FPGA-Computer/Automatic-Audio-Switch/Eagle CAD/LT Spice Simulation/ADC scaling & filter.asc

C1: cap; 1n8
R1: res; 10K
R2: res; 10K
V1: voltage; SINE(0 3.3V 1000); AC 1
V2: voltage; 3.3V
Named nets: 0, vout
;tran 5ms
.ac dec 1000 1 1e6
