FPGA-Computer/Automatic-Audio-Switch/STM32F030/intfft.c

/*------------------------------------------------------------------------/
/  Integer DFT module
/-------------------------------------------------------------------------/
/
/  Copyright (C) 2010, ChaN, all right reserved.
/
/ * This software is a free software and there is NO WARRANTY.
/ * No restriction on use. You can use, modify and redistribute it for
/   personal, non-profit or commercial products UNDER YOUR RESPONSIBILITY.
/ * Redistributions of source code must retain the above copyright notice.
/
/-------------------------------------------------------------------------*/


#include "intfft.h"

const uint16_t Tbl_brev[] = {
#if   N_FFT == 64
	0,32,16,48,8,40,24,56,4,36,20,52,12,44,28,60,2,34,18,50,10,42,26,58,6,38,22,54,14,46,30,62
#elif N_FFT == 128
	0,64,32,96,16,80,48,112,8,72,40,104,24,88,56,120,4,68,36,100,20,84,52,116,12,76,44,108,28,92,60,124,2,66,34,98,18,82,50,114,10,74,42,106,26,90,58,122,6,70,38,102,22,86,54,118,14,78,46,110,30,94,62,126
#elif N_FFT == 256
	0,128,64,192,32,160,96,224,16,144,80,208,48,176,112,240,8,136,72,200,40,168,104,232,24,152,88,216,56,184,120,248,4,132,68,196,36,164,100,228,20,148,84,212,52,180,116,244,12,140,76,204,44,172,108,236,28,156,92,220,60,188,124,252,2,130,66,194,34,162,98,226,18,146,82,210,50,178,114,242,10,138,74,202,42,170,106,234,26,154,90,218,58,186,122,250,6,134,70,198,38,166,102,230,22,150,86,214,54,182,118,246,14,142,78,206,46,174,110,238,30,158,94,222,62,190,126,254
#elif N_FFT == 512
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
)
{
	uint32_t i, s;
	int32_t a, b;


	s = 0;
	do {
		i = 0;
		do {
			a = fftbuf[Tbl_brev[i] + s].r;
			b = fftbuf[Tbl_brev[i] + s].i;
			*outbuf++ = isqrt32((uint32_t)(a * a) + (uint32_t)(b * b));
		} while (++i < N_FFT / 2);
	} while (s--);
}
