FPGA-Computer/Automatic-Audio-Switch/STM32F030/font 5x8.c

/*
 * font 5x8.c
 *
 * Created: 09/07/2013 1:46:07 PM
 *  Author: K. C. Lee
 * Copyright (c) 2016 by K. C. Lee 
 
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
	If not, see http://www.gnu.org/licenses/gpl-3.0.en.html
 */ 
 
#include "font.h"

const uint8_t Font_5x8[]=
{ 
	// Special symbols
	0xee,0x45,0x85,0x45,0xee,		//	26 0x1a	am
	0xef,0x45,0x85,0x45,0xe2,		//	27 0x1b	pm
	0x1c,0x1c,0x3e,0x7f,0x00,		//	28 0x1c Speaker
	0x22,0x1c,0x00,0x00,0x00,		//	29 0x1d Sound Sporadic
	0x22,0x1c,0x41,0x22,0x1c,		//	30 0x1e Sound on
	0x24,0x12,0x24,0x12,0x09,		//	31 0x1f Sound loud 
	//-------------------------------------------
  0x00,0x00,0x00,0x00,0x00,		//	32	0x20	' '
  0x00,0x00,0x4F,0x00,0x00,		//	33	0x21	'!'
  0x00,0x07,0x00,0x07,0x00,		//	34	0x22	'"'
  0x14,0x7F,0x14,0x7F,0x14,		//	35	0x23	'#'
  0x24,0x2A,0x7F,0x2A,0x12,		//	36	0x24	'$'
  0x23,0x13,0x08,0x64,0x62,		//	37	0x25	'%'
  0x3A,0x45,0x4A,0x30,0x28,		//	38	0x26	'&'
  0x00,0x05,0x03,0x00,0x00,		//	39	0x27	'''
  0x00,0x1C,0x22,0x41,0x00,		//	40	0x28	'('
  0x00,0x41,0x22,0x1C,0x00,		//	41	0x29	')'
  0x22,0x14,0x7F,0x14,0x22,		//	42	0x2A	'*'
  0x08,0x08,0x3E,0x08,0x08,		//	43	0x2B	'+'
  0x00,0x50,0x30,0x00,0x00,		//	44	0x2C	','
  0x08,0x08,0x08,0x08,0x08,		//	45	0x2D	'-'
  0x00,0x60,0x60,0x00,0x00,		//	46	0x2E	'.'
  0x40,0x20,0x10,0x08,0x04,		//	47	0x2F	'/'
  0x3E,0x51,0x49,0x45,0x3E,		//	48	0x30	'0'
  0x00,0x42,0x7F,0x40,0x00,		//	49	0x31	'1'
  0x62,0x51,0x51,0x49,0x46,		//	50	0x32	'2'
  0x22,0x41,0x49,0x49,0x36,		//	51	0x33	'3'
  0x18,0x14,0x12,0x7F,0x10,		//	52	0x34	'4'
  0x47,0x45,0x45,0x45,0x39,		//	53	0x35	'5'
  0x3C,0x4A,0x49,0x49,0x30,		//	54	0x36	'6'
  0x03,0x01,0x79,0x05,0x03,		//	55	0x37	'7'
  0x36,0x49,0x49,0x49,0x36,		//	56	0x38	'8'
  0x06,0x49,0x49,0x29,0x1E,		//	57	0x39	'9'
  0x00,0x36,0x36,0x00,0x00,		//	58	0x3A	':'
  0x00,0x56,0x36,0x00,0x00,		//	59	0x3B	';'
  0x08,0x14,0x22,0x41,0x00,		//	60	0x3C	'<'
  0x14,0x14,0x14,0x14,0x14,		//	61	0x3D	'='
  0x00,0x41,0x22,0x14,0x08,		//	62	0x3E	'>'
  0x02,0x01,0x51,0x09,0x06,		//	63	0x3F	'?'
  0x32,0x49,0x79,0x41,0x3E,		//	64	0x40	'@'
  0x7C,0x12,0x11,0x12,0x7C,		//	65	0x41	'A'
  0x41,0x7F,0x49,0x49,0x36,		//	66	0x42	'B'
  0x1C,0x22,0x41,0x41,0x22,		//	67	0x43	'C'
  0x41,0x7F,0x41,0x41,0x3E,		//	68	0x44	'D'
  0x7F,0x49,0x49,0x49,0x41,		//	69	0x45	'E'
  0x7F,0x09,0x09,0x09,0x01,		//	70	0x46	'F'
  0x3E,0x41,0x49,0x49,0x3A,		//	71	0x47	'G'
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
 };
